O-Lidenbrock/Reminton-Num-1.1/Assets/Front Render.png

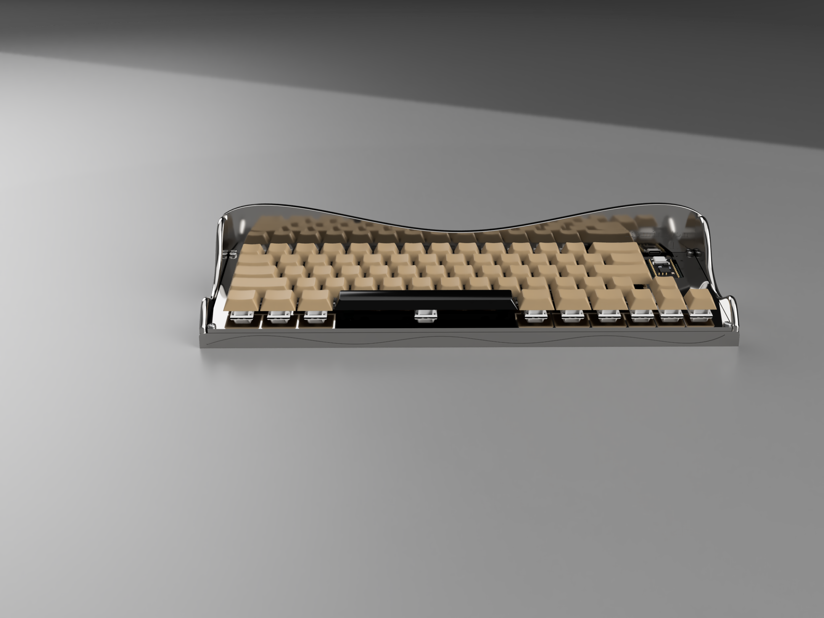
Assets/Front Render.png
