O-Lidenbrock/Reminton-Num-1.1/Assets/Lid_CAD.png

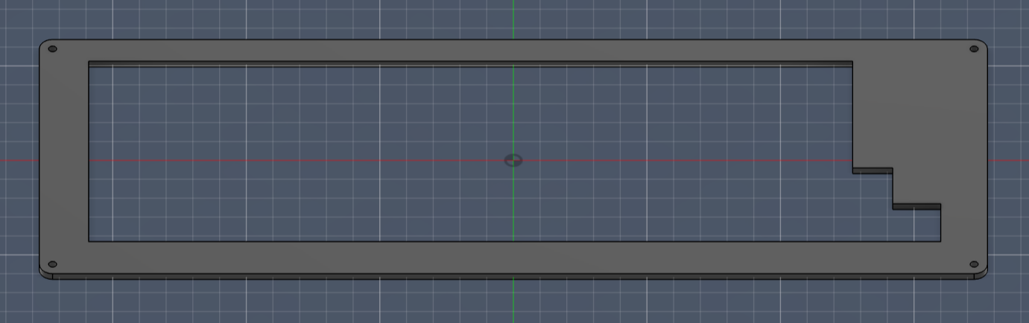
Assets/Lid_CAD.png
