O-Lidenbrock/Reminton-Num-1.1/Assets/render-2 transparent.png

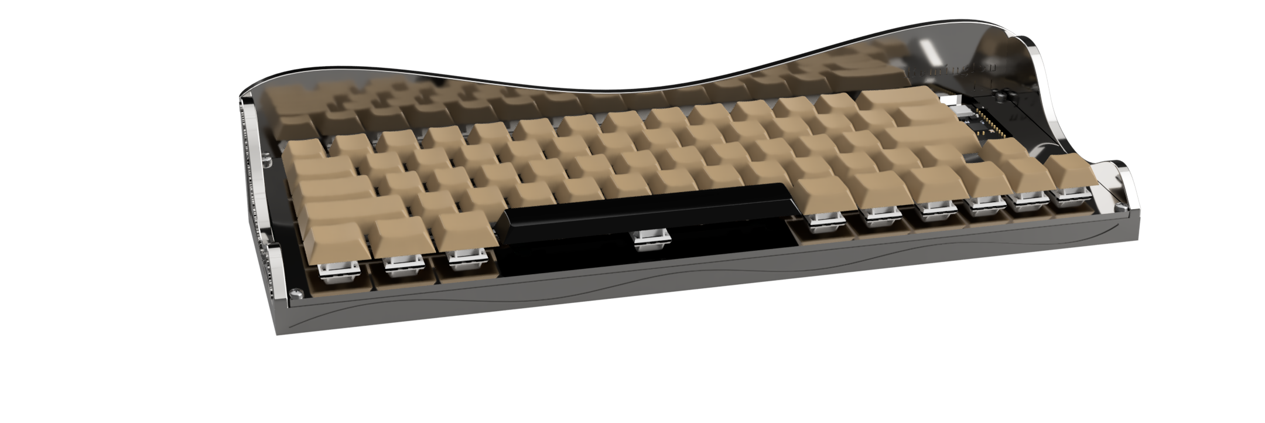
Assets/render-2 transparent.png
